adamzoiss/senior-design-312/src/managers/interface_manager.py

"""
Senior Project : Hardware Encryption Device
Team 312
File : interface_manager.py
Description: This will handle the interface with the rpi. GPIO pins will be set up
    and the interface will be handled through this class.
"""

import time


from src.handlers.display_handler import *
from handlers.gpio_handler import *
from src.managers.audio_manager import *
from src.logging.logger import *
from src.managers.thread_manager import ThreadManager
from src.managers.rf_manager import *


class InterfaceManager(GPIOHandler):
    """
    A class to manage the interface with the Raspberry Pi, including GPIO pins setup and handling.

    Attributes
    ----------
    position : int
        The current position for menu navigation.
    last_state_a : int
        The last state value for encoder A.
    last_state_b : int
        The last state value for encoder B.
    nav : DisplayHandler
        The navigation manager for the display.
    audio_man : AudioManager
        The audio manager for handling audio operations.

    Methods
    -------
    __init__(chip_number=0)
        Initializes the InterfaceManager with the given chip number.
    __del__()
        Cleans up resources and cancels callbacks.
    _encoder_callback(chip, gpio, level, timestamp)
        Handles the encoder callback events.
    _switch_callback(chip, gpio, level, timestamp)
        Handles the switch callback events.
    _init_callbacks()
        Initializes the GPIO callbacks.
    _cancel_callbacks()
        Cancels the GPIO callbacks.
    """

    def __init__(self, thread_manager: ThreadManager, chip_number=0):
        """
        Initializes the InterfaceManager with the given chip number.

        Parameters
        ----------
        chip_number : int, optional
            The chip number for the GPIO interface. Defaults to 0.
        """

        #################################################
        # Call base class constructor
        super().__init__(chip_number)
        #################################################
        # Create the thread manager
        self.thread_manager = thread_manager
        #################################################
        # Set up logging
        self.logger: logging = Logger(
            "InterfaceManager",
            overwrite=True,
            console_level=logging.INFO,
            console_logging=EN_CONSOLE_LOGGING,
        )
        #################################################
        # Import subprocess module to execute shell scripts

        log_msg = run_shell_script("$HOME/alsa_config_start.sh")
        self.logger.info(log_msg)
        ##################################################
        # Variable for volume
        self.volume = 100
        # Position variable for menu navigation
        self.position = -1
        # Last state values for the encoders
        self.last_state_a = 0
        self.last_state_b = 0
        ##################################################
        # Integrate audio
        try:
            self.audio_man = AudioManager(
                self.thread_manager,
                frame_size=FRAME_SIZE,
                format=FORMAT,
                channels=1,
                sample_rate=RATE,
                in_device_index=INPUT_DEV_INDEX,
                out_device_index=OUTPUT_DEV_INDEX,
            )
        except Exception as e:
            self.logger.critical(
                f"Exception when initialing audio manager: {e}"
            )
        #################################################
        # Display set up
        try:
            self.display = SSD1306(thread_manager)
            self.nav = DisplayHandler(self.display)
            self.nav.display.clear_screen()
            self.nav.get_screen(Menu)
            self.nav.CURRENT_SCREEN.update_volume(self.volume)
            self.nav.display.refresh_display()
        except Exception as e:
            self.logger.critical(f"Exception when initialing display: {e}")
        ##################################################
        # Set up Transmitter
        try:
            self.transmitter = RFManager(
                self.handle, self.thread_manager, self.audio_man
            )
        except Exception as e:
            self.logger.critical(f"Exception when initialing transmitter: {e}")
        ##################################################
        # State that the manager initialized
        self.logger.info("InterfaceManager initialized")

    def __del__(self):
        """
        Cleans up resources and cancels callbacks.
        """
        super().__del__()

    def _encoder_callback(self, chip, gpio, level, timestamp):
        """
        Handles the encoder callback events.

        Parameters
        ----------
        chip : int
            The chip number.
        gpio : int
            The GPIO pin number.
        level : int
            The level of the GPIO pin.
        timestamp : int
            The timestamp of the event.
        """
        self.logger.debug(
            (
                f"Chip{chip} | GPIO{gpio} | level: {level} | "
                f"Position: {self.position}"
            )
        )

        # If in debug mode, do not allow encoder to change volume
        if isinstance(self.nav.CURRENT_SCREEN, Debug):
            return

        # Logic for encoder alerts
        if gpio == ENC_A:
            # Check for if the encoder has been moved counter-clockwise
            if self.last_state_a != level:
                ##############################################################
                # Lower the volume
                if self.volume > 0:
                    self.volume -= 5
                ##############################################################
        elif gpio == ENC_B:
            # Check for if the encoder has been moved clockwise
            if self.last_state_b != level:
                ##############################################################
                # Raise the volume
                if self.volume < 100:
                    self.volume += 5
                ##############################################################

        # Update last states for the encoders
        self.last_state_a = level
        self.last_state_b = level
        # Update menu selection
        self.nav.update_menu_selection(self.position)
        self.nav.CURRENT_SCREEN.update_volume(self.volume)
        self.audio_man.volume = self.volume
        self.nav.display.refresh_display()

    def _switch_callback(self, chip, gpio, level, timestamp):
        """
        Handles the switch callback events.

        Parameters
        ----------
        chip : int
            The chip number.
        gpio : int
            The GPIO pin number.
        level : int
            The level of the GPIO pin.
        timestamp : int
            The timestamp of the event.
        """

        self.logger.debug(
            (
                f"Chip{chip} | GPIO{gpio} | level: {level} | "
                f"Position: {self.position}"
            )
        )

        if gpio == SW_1:  # Select button
            try:
                # If in debug mode, do not allow selection
                if isinstance(self.nav.CURRENT_SCREEN, Debug):
                    return

                if isinstance(self.nav.CURRENT_SCREEN, Menu):
                    # Check if settings was selected.
                    if (
                        self.position
                        == self.nav.CURRENT_SCREEN.SELECTIONS["SETTINGS"]
                    ):
                        self.nav.display.clear_screen()

                        self.nav.get_screen(
                            Settings,
                            self.audio_man.crypto_manager.penc_en,
                            self.audio_man.crypto_manager.denc_en,
                        )
                        self.nav.CURRENT_SCREEN.update_volume(self.volume)
                        self.nav.display.refresh_display()
                        self.position = -1
                    # Check if mode was selected.
                    elif (
                        self.position
                        == self.nav.CURRENT_SCREEN.SELECTIONS["MODE"]
                    ):
                        self.nav.display.clear_screen()
                        self.nav.get_screen(
                            Mode,
                            self.audio_man.crypto_manager.mode_aes,
                            self.audio_man.crypto_manager.mode_rsa,
                            self.audio_man.crypto_manager.mode_hybrid,
                        )
                        self.nav.CURRENT_SCREEN.update_volume(self.volume)
                        self.nav.display.refresh_display()
                        self.position = -1  # Reset selection position
                elif isinstance(self.nav.CURRENT_SCREEN, Mode):
                    if (
                        self.position
                        == self.nav.CURRENT_SCREEN.SELECTIONS["AES"]
                    ):
                        if not self.audio_man.crypto_manager.mode_aes:
                            self.audio_man.crypto_manager.mode_aes = True
                            self.audio_man.crypto_manager.mode_rsa = False
                            self.audio_man.crypto_manager.mode_hybrid = False
                            self.logger.info("AES Mode Selected")
                    elif (
                        self.position
                        == self.nav.CURRENT_SCREEN.SELECTIONS["RSA"]
                    ):
                        if not self.audio_man.crypto_manager.mode_rsa:
                            self.audio_man.crypto_manager.mode_aes = False
                            self.audio_man.crypto_manager.mode_rsa = True
                            self.audio_man.crypto_manager.mode_hybrid = False
                            self.logger.info("RSA Mode Selected")
                    elif (
                        self.position
                        == self.nav.CURRENT_SCREEN.SELECTIONS["HYBRID"]
                    ):
                        if not self.audio_man.crypto_manager.mode_hybrid:
                            self.audio_man.crypto_manager.mode_aes = False
                            self.audio_man.crypto_manager.mode_rsa = False
                            self.audio_man.crypto_manager.mode_hybrid = True
                            self.logger.info("HYBRID Mode Selected")

                    # Update the display based on the selection.
                    self.nav.display.clear_screen()
                    self.nav.get_screen(
                        Mode,
                        self.audio_man.crypto_manager.mode_aes,
                        self.audio_man.crypto_manager.mode_rsa,
                        self.audio_man.crypto_manager.mode_hybrid,
                    )
                    self.nav.CURRENT_SCREEN.update_volume(self.volume)
                    self.nav.display.refresh_display()
                    self.position = -1

                    # self.nav.display.clear_screen()
                    # self.nav.get_screen(Debug)
                    # # self.nav.CURRENT_SCREEN.update_volume(self.volume)
                    # self.nav.display.display_image()
                    # self.position = -1  # Reset selection position

                    # self.thread_manager.start_thread(
                    #     "Debug", self.nav.CURRENT_SCREEN.display_debug_info
                    # )
                elif isinstance(self.nav.CURRENT_SCREEN, Settings):
                    # Toggling encryption
                    if (
                        self.position
                        == self.nav.CURRENT_SCREEN.SELECTIONS["PENC"]
                    ):
                        self.nav.display.clear_screen()
                        self.audio_man.crypto_manager.penc_en = (
                            not self.audio_man.crypto_manager.penc_en
                        )
                        # If encryption is enabled, set the encryption key
                        if self.audio_man.crypto_manager.penc_en:
                            self.transmitter.rfm69.encryption_key = (
                                ENCRYPTION_KEY
                            )
                            self.logger.info("Packet Encryption Enabled")
                        # If encryption is disabled, set the encryption key to None
                        else:
                            self.transmitter.rfm69.encryption_key = None
                            self.logger.info("Packet Encryption Disabled")

                        # Update the display
                        self.nav.get_screen(
                            Settings,
                            self.audio_man.crypto_manager.penc_en,
                            self.audio_man.crypto_manager.denc_en,
                        )
                        self.nav.CURRENT_SCREEN.update_volume(self.volume)
                        self.nav.display.refresh_display()
                        self.position = -1

                    elif (
                        self.position
                        == self.nav.CURRENT_SCREEN.SELECTIONS["DENC"]
                    ):
                        self.nav.display.clear_screen()
                        self.audio_man.crypto_manager.denc_en = (
                            not self.audio_man.crypto_manager.denc_en
                        )
                        if self.audio_man.crypto_manager.denc_en:
                            self.logger.info("Data Encryption Enabled")
                        else:
                            self.logger.info("Data Encryption Disabled")

                        # Update the display
                        self.nav.get_screen(
                            Settings,
                            self.audio_man.crypto_manager.penc_en,
                            self.audio_man.crypto_manager.denc_en,
                        )
                        self.nav.CURRENT_SCREEN.update_volume(self.volume)
                        self.nav.display.refresh_display()
                        self.position = -1
                else:
                    pass
            except KeyError:
                # Excepting a key error if the selection is not found,
                # this is to prevent the program from crashing
                pass

        elif gpio == SW_2:  # Down arrow
            # If in debug mode, do not allow selection
            if isinstance(self.nav.CURRENT_SCREEN, Debug):
                return

            # Upper bound for valid selection position
            if self.position < len(self.nav.CURRENT_SCREEN.SELECTIONS) - 1:
                self.position += 1

            # Update menu selection
            self.nav.update_menu_selection(self.position)
            self.nav.CURRENT_SCREEN.update_volume(self.volume)
            self.nav.display.refresh_display()

        elif gpio == SW_3:  # TX / Monitor button
            # If in debug mode, do not allow selection
            if isinstance(self.nav.CURRENT_SCREEN, Debug):
                return

            # Checks if switch is pressed, and if so monitors audio
            # TODO Have tx rx implementation
            try:
                match level:
                    case 0:  # Button pressed
                        self.thread_manager.start_thread(
                            TRANSMIT_THREAD,
                            self.transmitter.handle_input_stream,
                        )
                    case 1:  # Button released
                        # Stop the transmit thread
                        self.thread_manager.stop_thread(TRANSMIT_THREAD)
                        # Set the transmitter to be able to receive again.
                        self.transmitter.rfm69.listen()
                    case _:  # Default case
                        self.logger.error("Error GPIO level is not 0 or 1")
            except Exception as e:
                self.logger.error(f"Error with exception: {e}")

        elif gpio == SW_4:  # Up arrow
            # If in debug mode, do not allow selection
            if isinstance(self.nav.CURRENT_SCREEN, Debug):
                return

            # Lower bound for valid selection position
            if self.position >= 0:
                self.position -= 1

            # Update menu selection
            self.nav.update_menu_selection(self.position)
            self.nav.CURRENT_SCREEN.update_volume(self.volume)
            self.nav.display.refresh_display()

        elif gpio == SW_5:  # Return arrow
            self.thread_manager.stop_all_threads()
            # Checks if the return arrow option is pressed and returns to menu
            if type(self.nav.CURRENT_SCREEN) != Menu:
                self.nav.display.clear_screen()
                self.nav.get_screen(Menu)
                self.nav.CURRENT_SCREEN.update_volume(self.volume)
                self.nav.display.refresh_display()
                self.position = -1  # Reset selection position


if __name__ == "__main__":
    import signal

    try:
        thread_manager = ThreadManager()
        interface = InterfaceManager(thread_manager)

        while True:
            time.sleep(1)
    except KeyboardInterrupt:
        interface.logger.info("\nExiting Program...\n")
    finally:
        interface.thread_manager.stop_all_threads()
        interface.nav.display.clear_and_turn_off()
        interface.logger.info("Successfully Exited.")
